soundslikefrank/grow/include/uart_debug.h

/**
 * Uses huart1 for communication via the internal st-link
 */
#include <stm32l4xx_hal.h>

#ifndef SRC_UART_DEBUG_H_
  #define SRC_UART_DEBUG_H_

UART_HandleTypeDef huart1;

void HUART1_Init(void) {
  // Initialize USART1
  huart1.Instance = USART1;
  huart1.Init.BaudRate = 38400;
  huart1.Init.WordLength = UART_WORDLENGTH_8B;
  huart1.Init.StopBits = UART_STOPBITS_1;
  huart1.Init.Parity = UART_PARITY_NONE;
  huart1.Init.Mode = UART_MODE_TX_RX;
  huart1.Init.HwFlowCtl = UART_HWCONTROL_NONE;
  huart1.Init.OverSampling = UART_OVERSAMPLING_16;
  huart1.Init.OneBitSampling = UART_ONE_BIT_SAMPLE_DISABLE;
  huart1.AdvancedInit.AdvFeatureInit = UART_ADVFEATURE_NO_INIT;
  HAL_UART_Init(&huart1);
}

extern "C" {
/**
 * @brief UART MSP Initialization
 * This function configures the hardware resources used in this example
 * @param huart: UART handle pointer
 * @retval None
 */
void HAL_UART_MspInit(UART_HandleTypeDef* huart) {
  GPIO_InitTypeDef gpio = {0};
  if (huart->Instance == USART1) {
    /* Peripheral clock enable */
    __HAL_RCC_USART1_CLK_ENABLE();

    __HAL_RCC_GPIOA_CLK_ENABLE();
    /**USART1 GPIO Configuration
    PA9     ------> USART1_TX
    PA10     ------> USART1_RX
    */
    gpio.Pin = GPIO_PIN_9 | GPIO_PIN_10;
    gpio.Mode = GPIO_MODE_AF_PP;
    gpio.Pull = GPIO_NOPULL;
    gpio.Speed = GPIO_SPEED_FREQ_HIGH;
    gpio.Alternate = GPIO_AF7_USART1;
    HAL_GPIO_Init(GPIOA, &gpio);
  }
}
}

#endif  // SRC_UART_DEBUG_H_
