soundslikefrank/grow/include/conf.h

// Copyright 2020 Christian Maniewski <code@chmanie.com>

#ifndef CONF_H
#define CONF_H

enum InputJack {
  INPUT_JACK_TRIGGER,
  INPUT_JACK_CV_1,
  INPUT_JACK_CV_2,
  INPUT_JACK_LAST,
};

#endif  // CONF_H
