soundslikefrank/grow/src/sequencer.cpp

// Copyright 2020 Christian Maniewski.

#include "sequencer.h"
#include <stm32l4xx_hal.h>
#include "drivers/fader_led.h"
#include "drivers/tim_metronome.h"

SequencerClass::SequencerClass() = default;

void SequencerClass::Init() { /* @TODO Do we need to do anything here? */
}

void SequencerClass::Start() { running_ = true; }

void SequencerClass::Stop() { running_ = false; }

uint8_t SequencerClass::NextStep() {
  if (!running_) {
    return currentStep_;
  }
  if (currentStep_ < stepLength_ - 1) {
    currentStep_++;
  } else {
    currentStep_ = 0;
  }
  FaderLED.SetPosition(currentStep_ % 8);
  return currentStep_;
}

void SequencerClass::SetStepLength(uint8_t stepLength) {
  if (stepLength > 64) {
    stepLength_ = 64;
  } else if (stepLength < 0) {
    stepLength_ = 0;
  } else {
    stepLength_ = stepLength;
  }
}

SequencerClass Sequencer;
